Solderingironspb/Keyboard-for-PUBG/images/photo (1).jpg

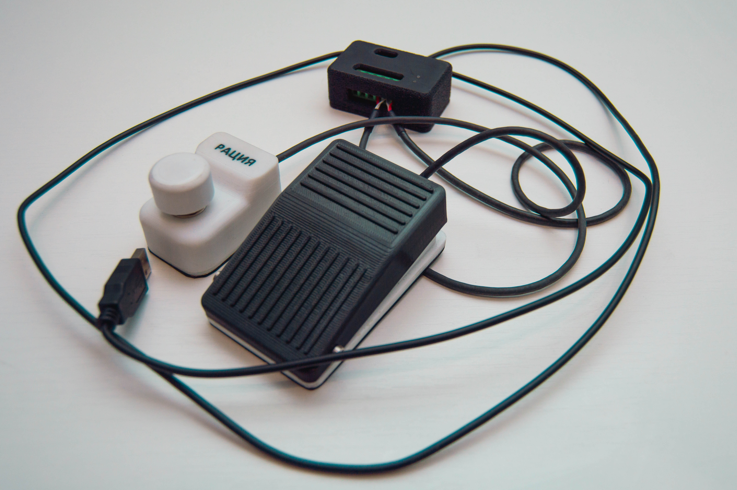
images/photo (1).jpg
