Solderingironspb/Keyboard-for-PUBG/images/photo (2).jpg

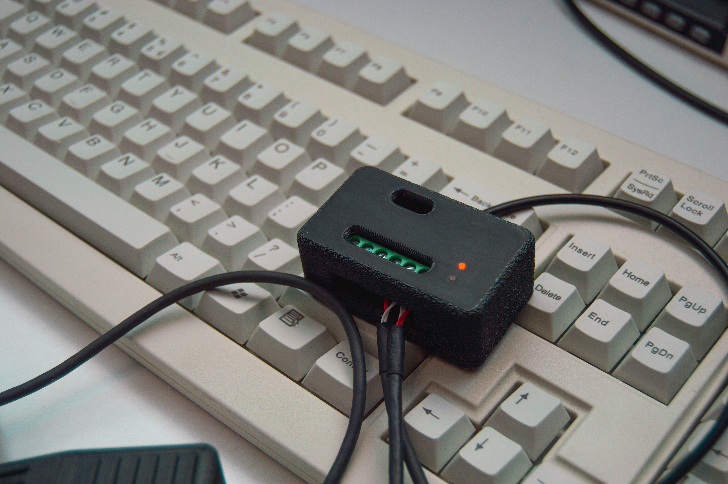
images/photo (2).jpg
